kishankrs/KUINO/28Pins_Project_V1I1/!Released Files/Step 2 - Board Assembly/[Variant 1 - 28Pins V1I1 - FIXED 5V]/Top View Drawing - 28Pins V1I1 - FIXED 5V.PDF

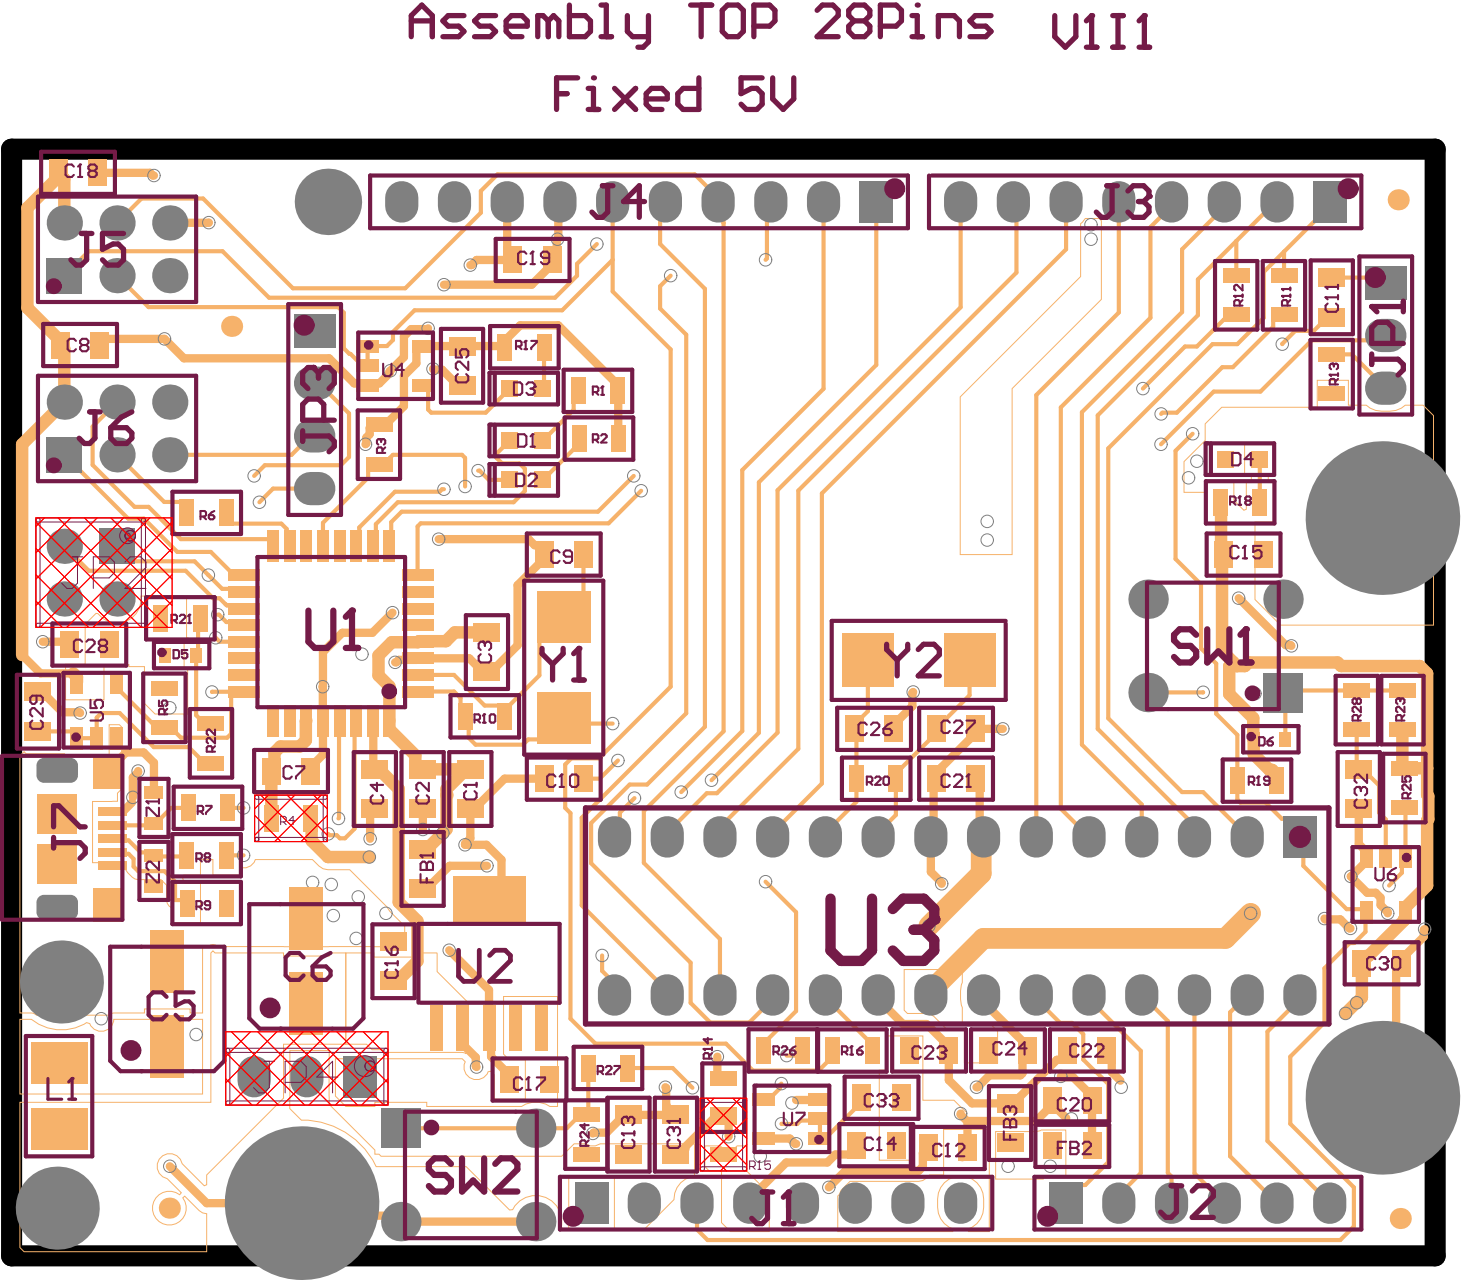
[picture p13: page 1]
