kishankrs/KUINO/28Pins_Project_V1I1/!Released Files/Step 2 - Board Assembly/[Variant 2 - 28Pins V1I1 - 5V AND 3V3]/Top View Drawing - 28Pins V1I1 - 5V AND 3V3.PDF

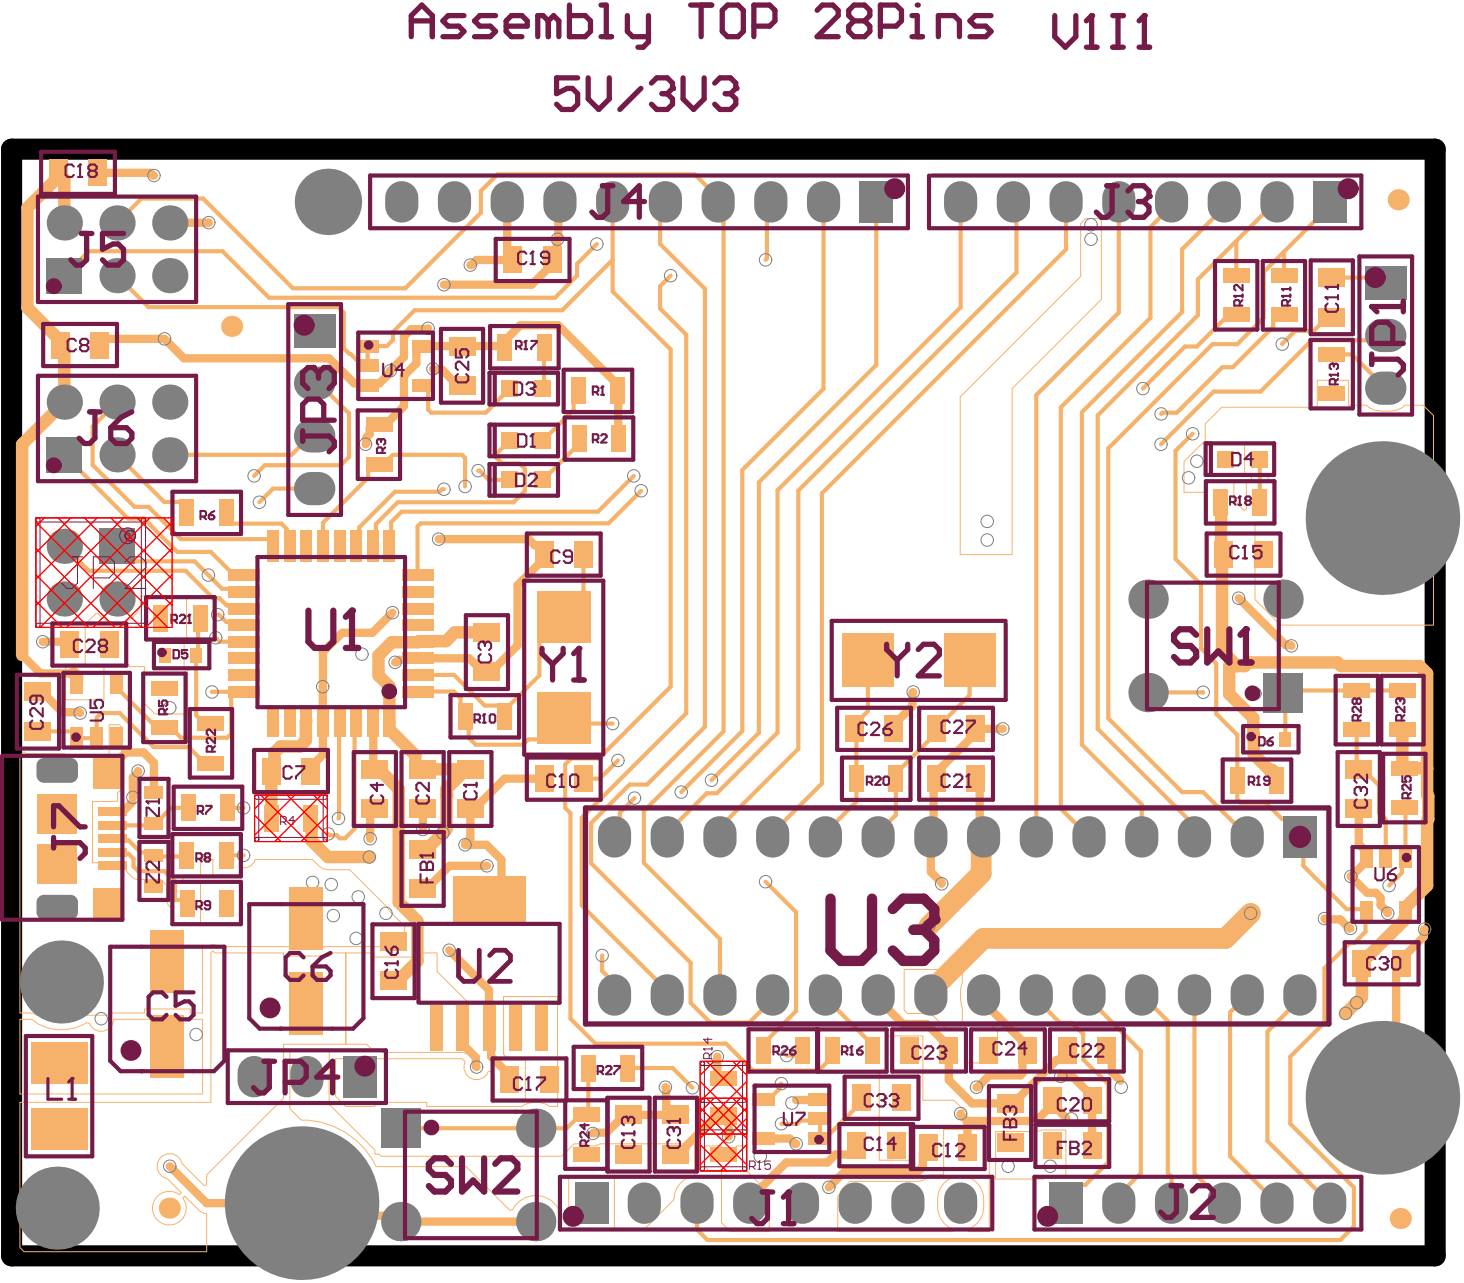
[picture p14: page 1]
