kishankrs/KUINO/28Pins_Project_V1I1/!Released Files/Step 1 - PCB Manufacturing/NC Drill Output/28Pins Drill Drawing.PDF

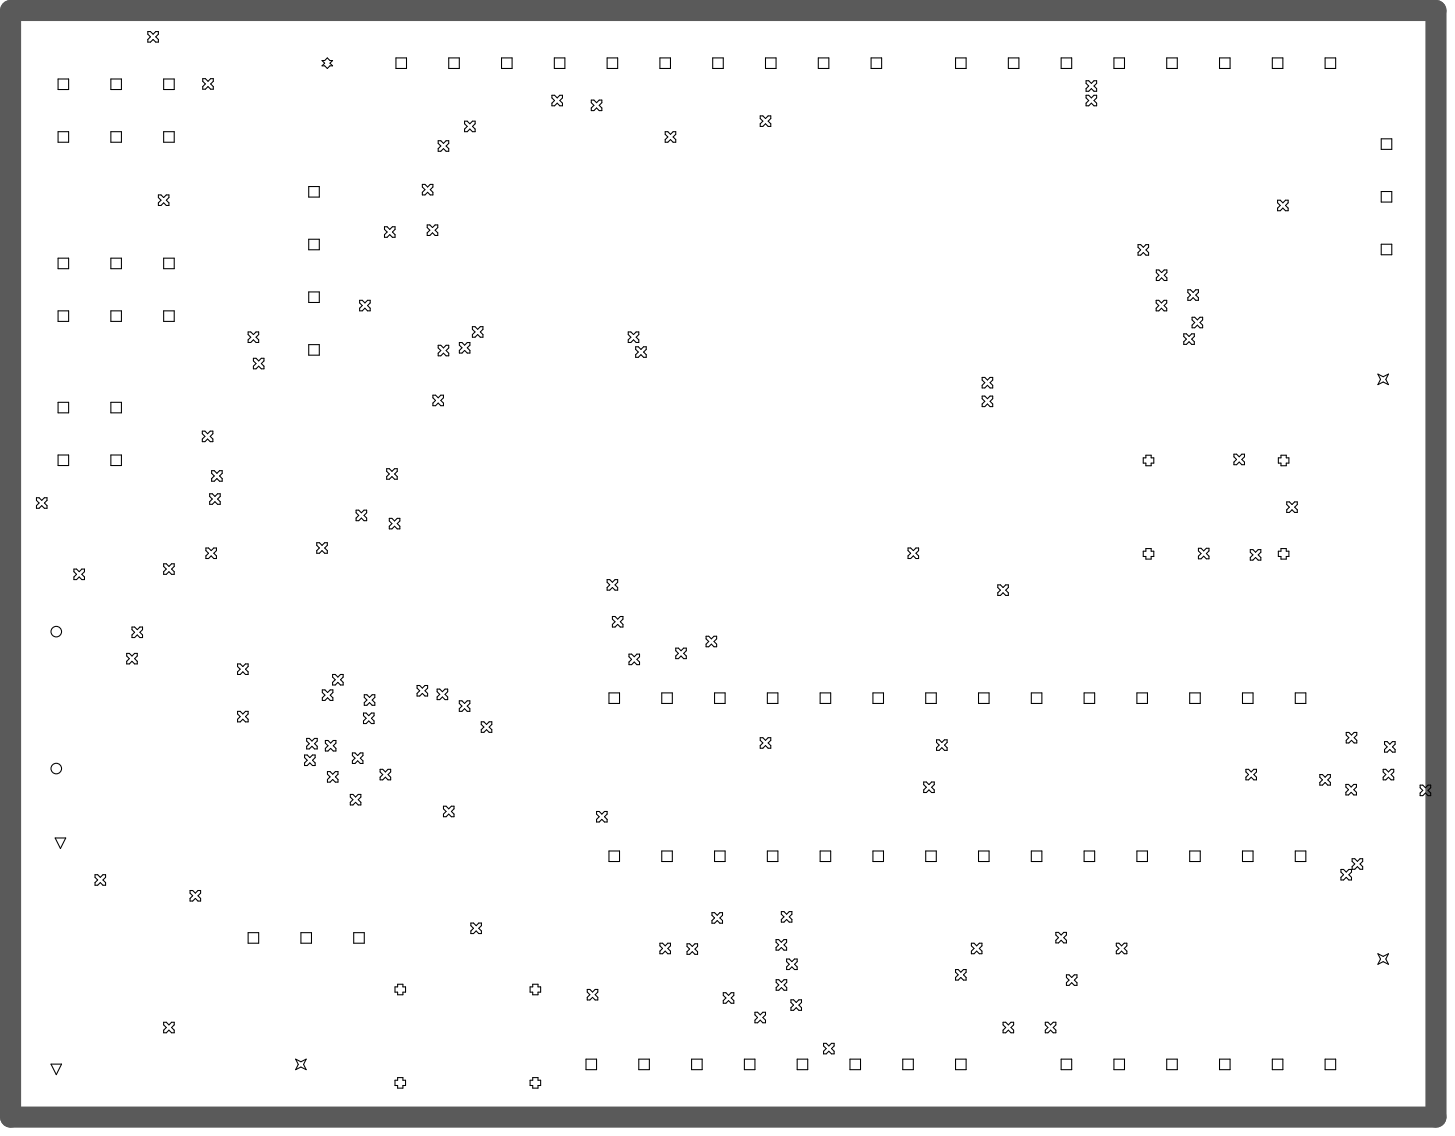
[picture p15: page 1]

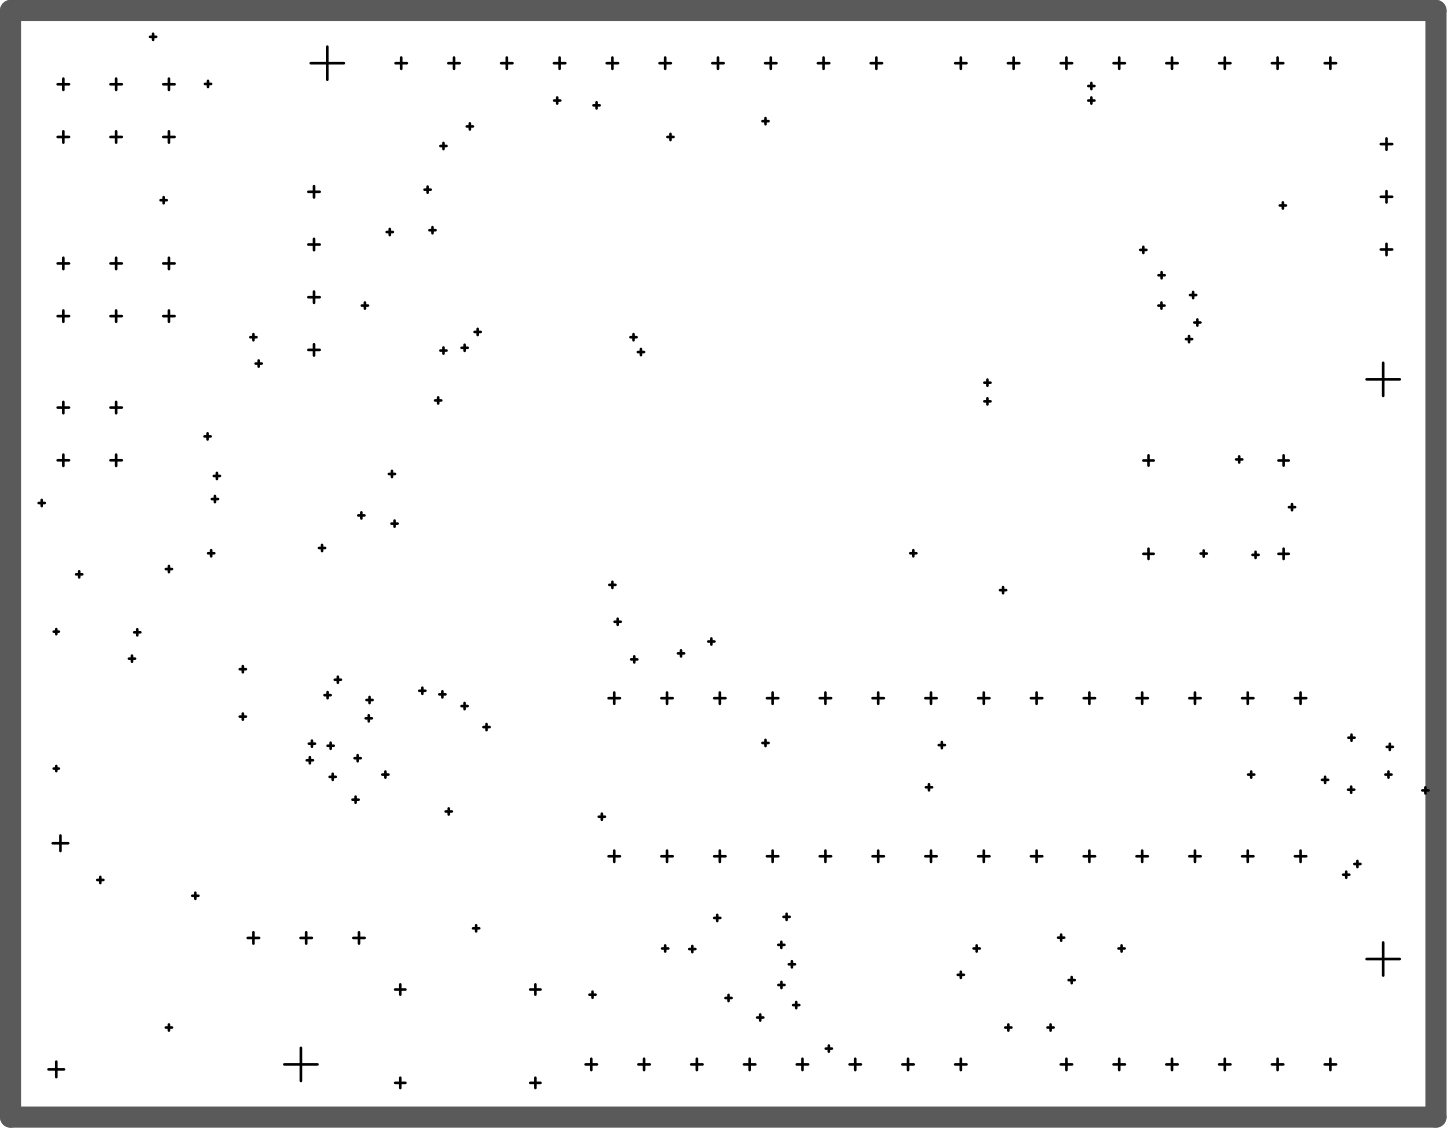
[picture p16: page 2]
